artekw/matrixblock/HT1632c.h

#include <stdint.h>
#include <time.h>
#include "MMAP/mmapgpio.h"

#define _NOP() do { __asm__ __volatile__ ("nop"); } while (0)

// http://leaflabs.com/docs/arm-gcc.html
typedef const unsigned char prog_uchar;
#define pgm_read_byte_near(x) (*(prog_uchar*)x)
#define pgm_read_byte(x) (*(prog_uchar*)x)
#define bitRead(value, bit) (((value) >> (bit)) & 0x01)

/*
 * commands written to the chip consist of a 3 bit "ID", followed by
 * either 9 bits of "Command code" or 7 bits of address + 4 bits of data.
 */

#define HT1632_ID_CMD 4   /* ID = 100 - Commands */
#define HT1632_ID_RD  6   /* ID = 110 - Read RAM */
#define HT1632_ID_WR  5   /* ID = 101 - Write RAM */
#define HT1632_ID_BITS (1<<2)   /* IDs are 3 bits */

#define HT1632_CMD_SYSDIS 0x00  /* CMD= 0000-0000-x Turn off oscil */
#define HT1632_CMD_SYSON  0x01  /* CMD= 0000-0001-x Enable system oscil */
#define HT1632_CMD_LEDOFF 0x02  /* CMD= 0000-0010-x LED duty cycle gen off */
#define HT1632_CMD_LEDON  0x03  /* CMD= 0000-0011-x LEDs ON */
#define HT1632_CMD_BLOFF  0x08  /* CMD= 0000-1000-x Blink ON */
#define HT1632_CMD_BLON   0x09  /* CMD= 0000-1001-x Blink Off */
#define HT1632_CMD_SLVMD  0x10  /* CMD= 0001-00xx-x Slave Mode */
#define HT1632_CMD_MSTMD  0x14  /* CMD= 0001-01xx-x Master Mode */
#define HT1632_CMD_RCCLK  0x18  /* CMD= 0001-10xx-x Use on-chip clock */
#define HT1632_CMD_EXTCLK 0x1C  /* CMD= 0001-11xx-x Use external clock */
#define HT1632_CMD_COMS00 0x20  /* CMD= 0010-ABxx-x commons options */
#define HT1632_CMD_COMS01 0x24  /* CMD= 0010-ABxx-x commons options */
#define HT1632_CMD_COMS10 0x28  /* CMD= 0010-ABxx-x commons options */
#define HT1632_CMD_COMS11 0x2C  /* CMD= 0010-ABxx-x commons options */
#define HT1632_CMD_PWM    0xA0  /* CMD= 101x-PPPP-x PWM duty cycle */
#define HT1632_CMD_BITS (1<<7)

#define CLK_DELAY _NOP()


// possible values for a pixel;
#define BLACK  0
#define GREEN  1
#define RED    2
#define ORANGE 3

// insert here the number of columns of your font files
// the compiler will comment how large the number of columns
// should be
#define NCOLUMNS 8

#define DELAY 1000

#define plot(x,y,v)  ht1632_plot(x,y,v)
//#define cls          ht1632_clear
#define clearScreen  ht1632_clear

//**************************************************************************************************
//Function Name: calcBit
//Function Feature: calculate the bitval of y
//Input Argument: y: Y coordinate
//Output Argument: bitval
//**************************************************************************************************
#define calcBit(y) (8>>(y&3))

/*
 *  Class definition
 */
class HT1632c {

  public:
      // constructor
      HT1632c(char bank, char da, char wr, char cs, char cl);
      HT1632c(char bank, char a, char da, char wr, char cs, char cl);

      char bank;

      /*
       * Set these variable to the values of the pins connected to the SureElectronics Module
       */
      char ht1632_data;  // Data pin
      char ht1632_wrclk; // Write clock pin
      char ht1632_cs;    // Chip Select
      char ht1632_clk;   // clock pin

      /*
       * how many displays, chips and max size?
       */
      char Number_of_Displays;
      char CHIP_MAX; // 4*Number_of_Displays, Four HT1632Cs on one board
      char X_MAX; // 32*Number_of_Displays
      char Y_MAX; // 16

      // original functions
      void OutputCLK_Pulse(void); //Output a clock pulse
      void OutputA_74164(char x); //Input a digital level to 74164
      void ChipSelect(int select);
      void ht1632_writebits (uint8_t bits, uint8_t firstbit);
      void ht1632_sendcmd (char chipNo, uint8_t command);
      void ht1632_senddata (char chipNo, uint8_t address, uint8_t data);
      void ht1632_setup();
      char xyToIndex(char x, char y);
      int get_pixel(char x, char y);
      void ht1632_plot (char x, char y, char color);
      void ht1632_clear();
      void set_brightness(char pwm);
      void ht1632_putchar(int x, int y, char c, char color=GREEN);
      void scrolltextxcolor(int y,char Str1[ ], char color, int delaytime);

      void setup();
      void cls();
      void putChar(char c, int x, int y, char color=GREEN);
      void text(char str[], int x, int y, int color=ORANGE);
      void text(int num, int x, int y, int color=GREEN);

    private:
      GPIO_MMAP *gpiobank;
      unsigned char ht1632_shadowram[64][4*2];

      int numdigits(int n);
      int extractDigit(int number, int place);
      struct timespec ts;
};
